wcelina/3-in-1-Console-411FA22_Group3-/product_design/411_design_sketch.png

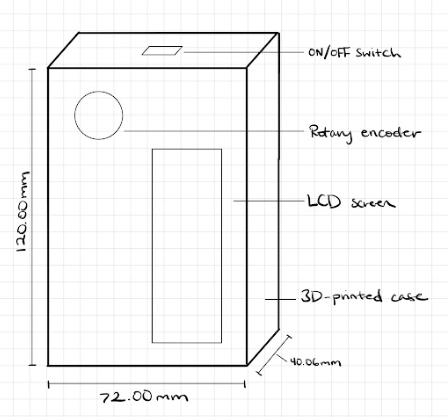
product_design/411_design_sketch.png
